hallard/RFM12B-BreakOut/RFM12B-V1.1-bottom.png

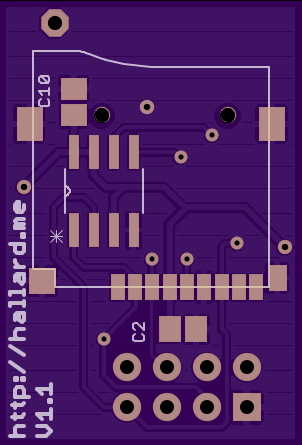
RFM12B-V1.1-bottom.png
