hallard/RFM12B-BreakOut/RFM12B-V1.1-top.png

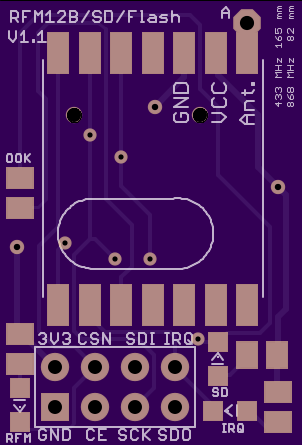
RFM12B-V1.1-top.png
