hallard/RFM12B-BreakOut/RFM12B-V1.2-sch.png

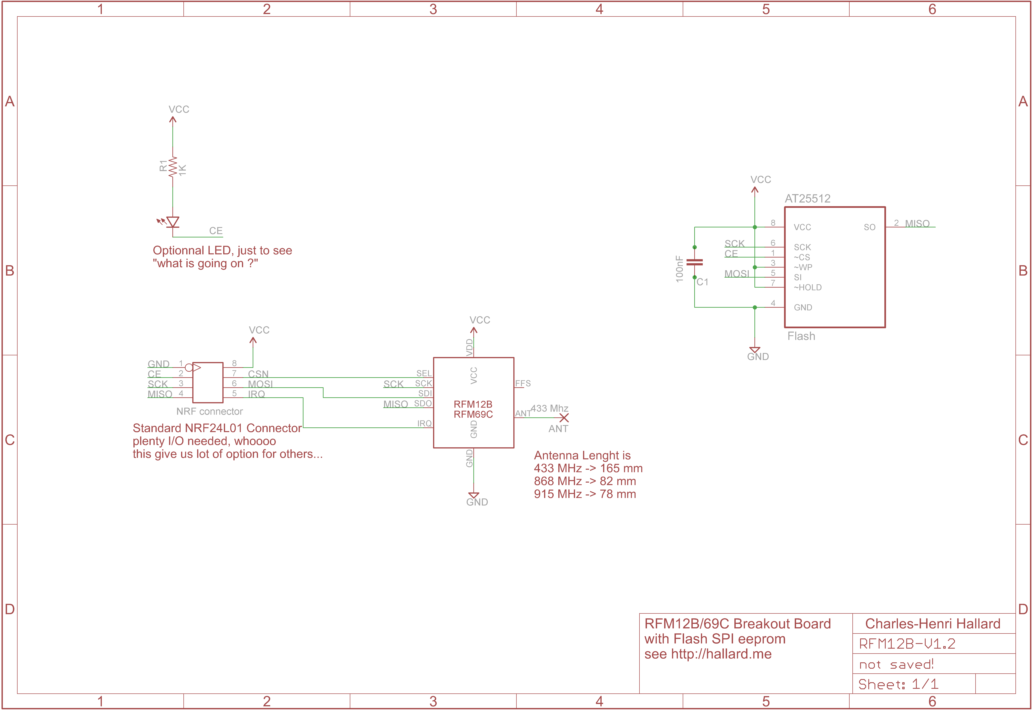
RFM12B-V1.2-sch.png
