hallard/RFM12B-BreakOut/RFM12B-V1.2-SMD-bottom.png

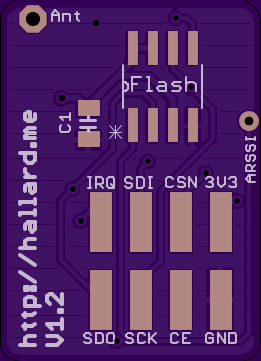
RFM12B-V1.2-SMD-bottom.png
