hallard/RFM12B-BreakOut/RFM12B-V1.2-SMD-top.png

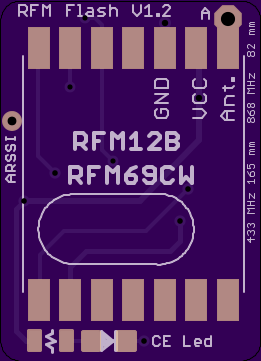
RFM12B-V1.2-SMD-top.png
